johnpolakow/PI_Blackbox/Docs/Diagrams/Single_Pi.pdf

## Single Raspberry Pi

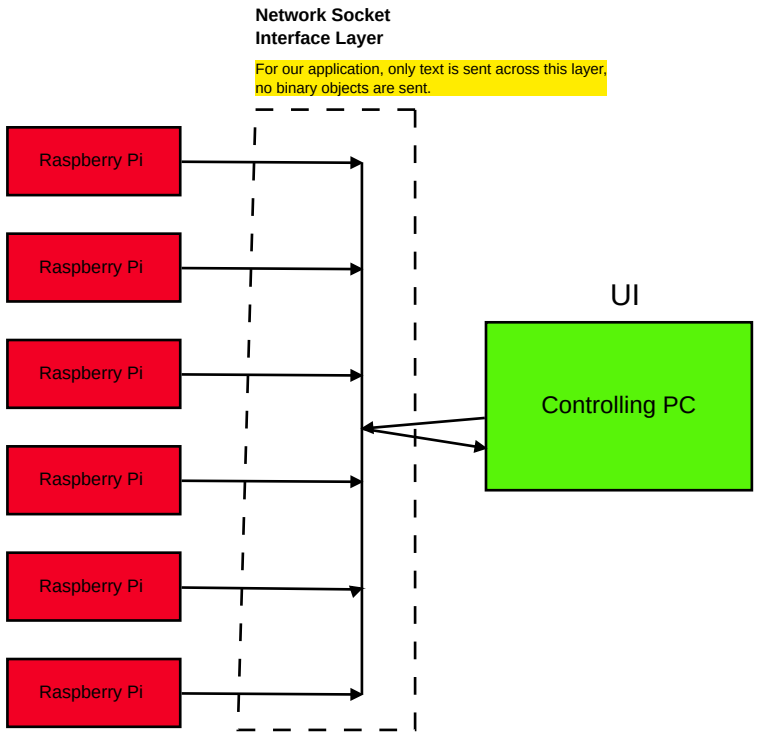
[picture p5: figure]
Raspberry Pi; Controlling PC; Network Socket Interface Layer; no binary objects are sent.

## Controlling PC

## Pis networked together via Ethernet or Wifi

For our application, only text is sent across this layer,

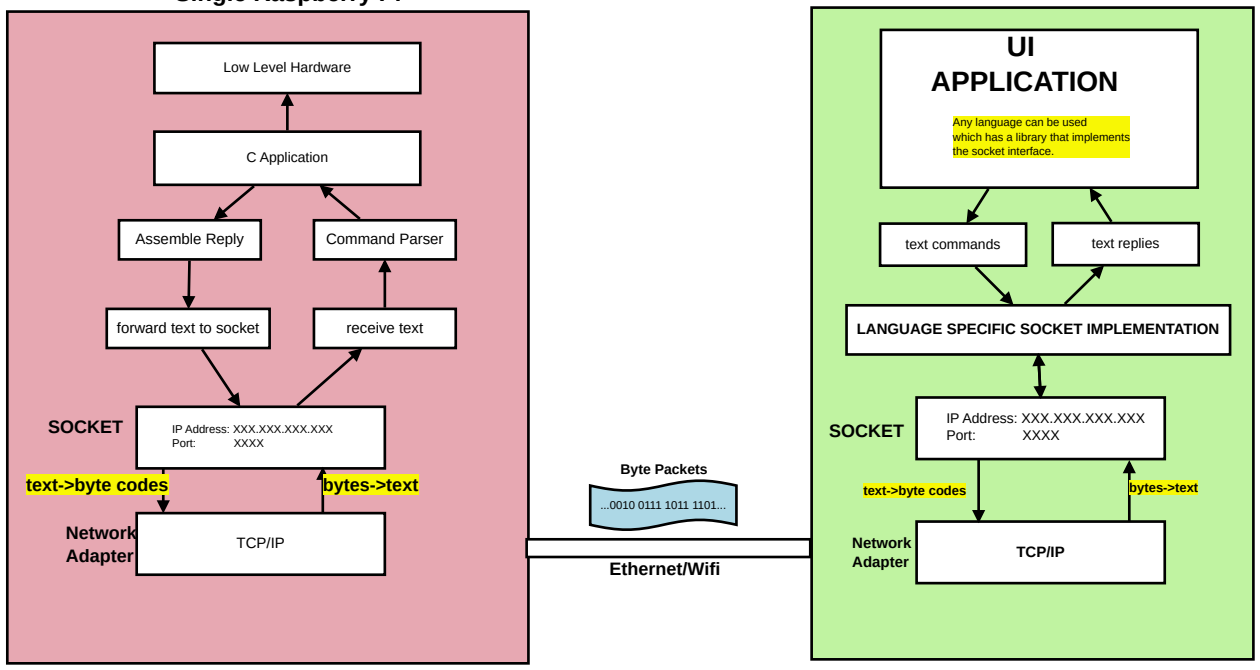
[picture p6: figure]
Low Level Hardware; C Application; Command Parser; receive text; Assemble Reply; forward text to socket; SOCKET; IP Address: XXX.XXX.XXX.XXX; Port:; XXXX; TCP/IP Network Adapter; text->byte codes; TCP/IP; bytes->text; Network Adapter; Byte Packets; Ethernet/Wifi; UI APPLICATION; text commands; text replies; LANGUAGE SPECIFIC SOCKET IMPLEMENTATION; Any language can be used which has a library that implements the socket interface.
