johnpolakow/PI_Blackbox/md/netstat_l_46.png

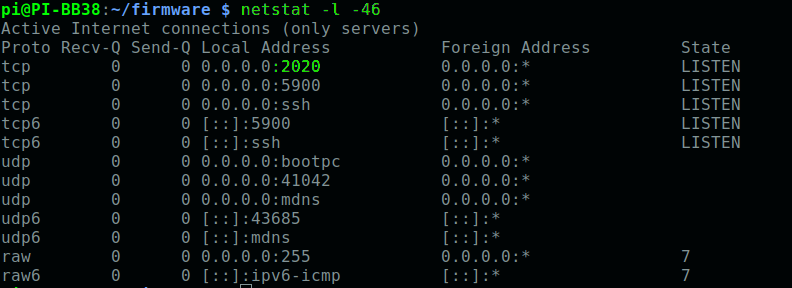
md/netstat_l_46.png
