johnpolakow/PI_Blackbox/PI_Firmware/Configuration/conf_files/images/72.jpeg

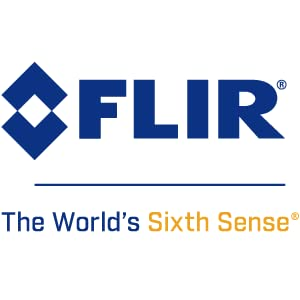
PI_Firmware/Configuration/conf_files/images/72.jpeg
