johnpolakow/PI_Blackbox/PI_Firmware/Configuration/conf_files/images/BlackPi.jpg

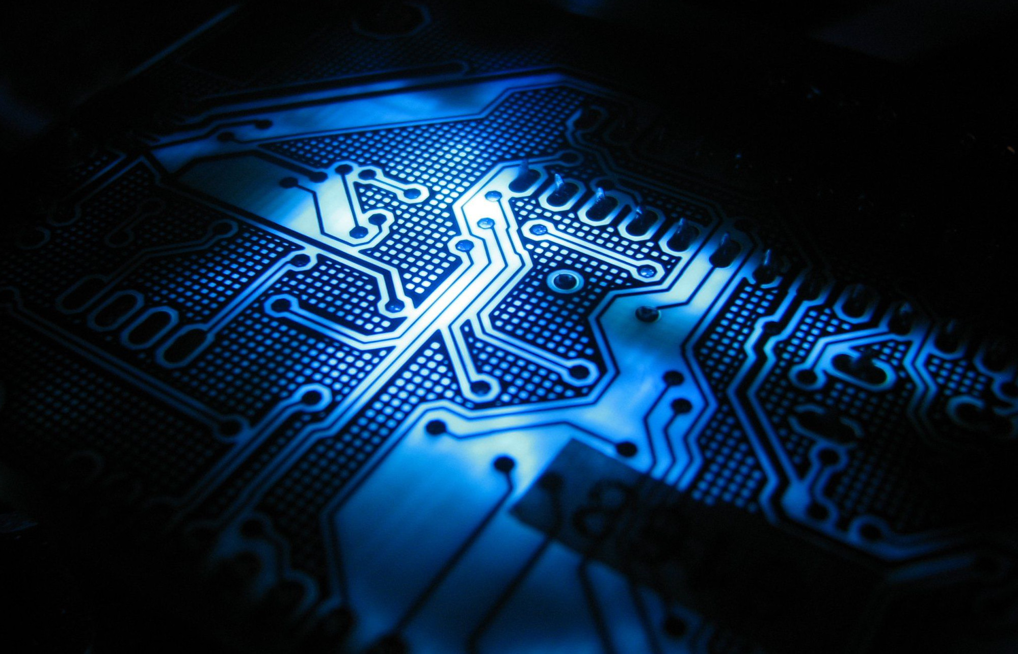
PI_Firmware/Configuration/conf_files/images/BlackPi.jpg
