johnpolakow/PI_Blackbox/PI_Firmware/Configuration/conf_files/images/geometry.jpg

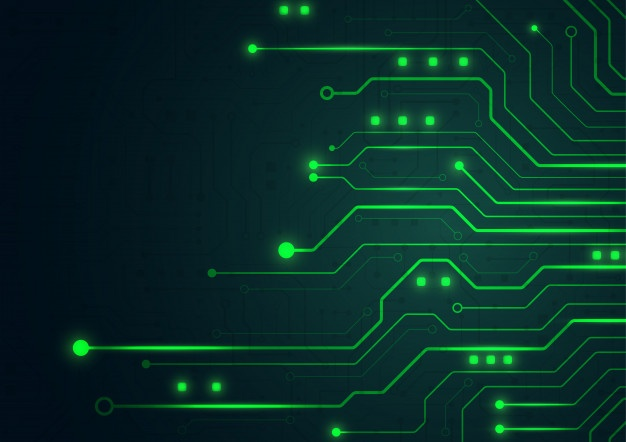
PI_Firmware/Configuration/conf_files/images/geometry.jpg
