johnpolakow/PI_Blackbox/PI_Firmware/Configuration/conf_files/images/glow2pi.jpg

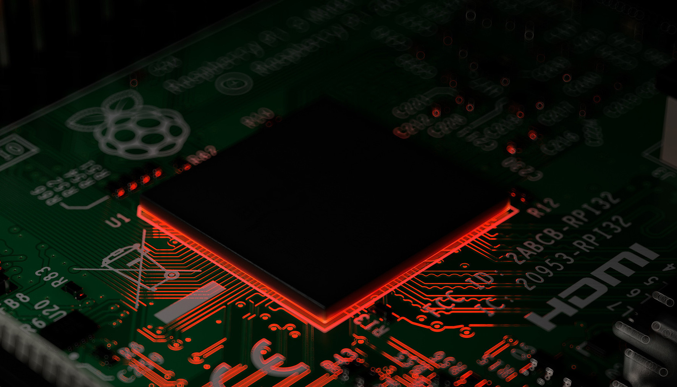
PI_Firmware/Configuration/conf_files/images/glow2pi.jpg
