johnpolakow/PI_Blackbox/PI_Firmware/Configuration/conf_files/images/landscape.png

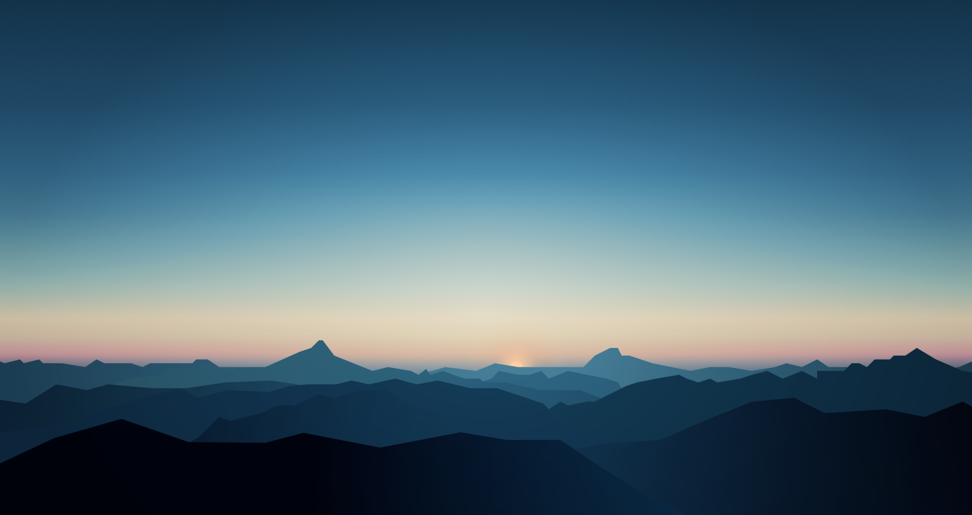
PI_Firmware/Configuration/conf_files/images/landscape.png
