johnpolakow/PI_Blackbox/PI_Firmware/Configuration/conf_files/images/unnamed1.jpg

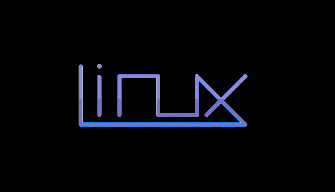
PI_Firmware/Configuration/conf_files/images/unnamed1.jpg
