johnpolakow/PI_Blackbox/PCB/Cal_Station/Cal_Station.pdf

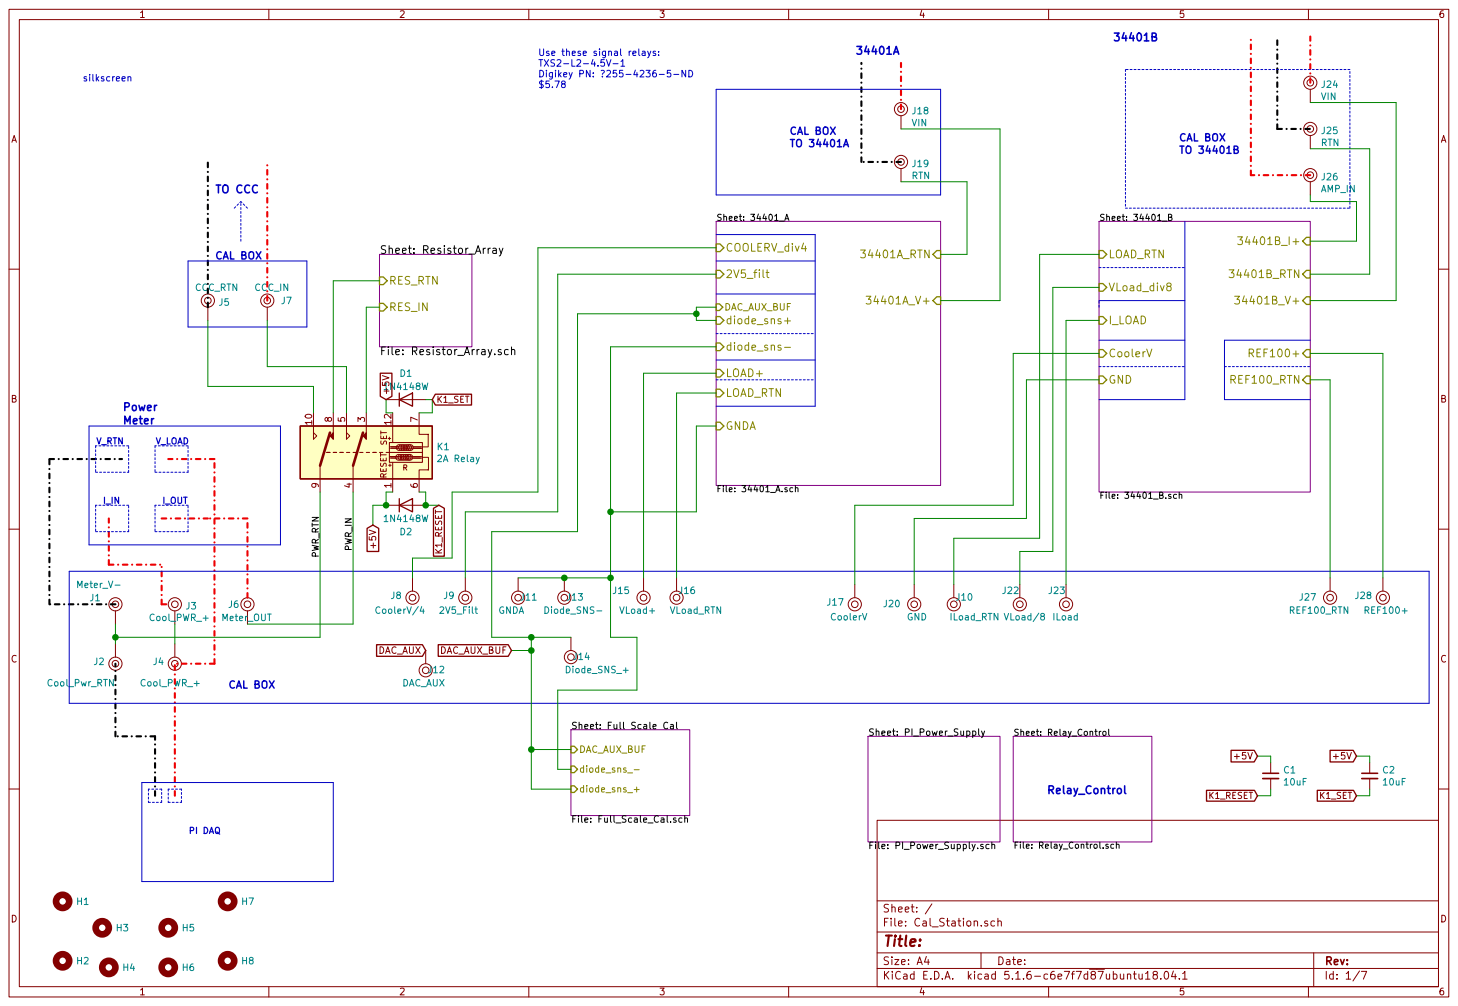
[picture p33: page 1]

CAL BOX

34401A_V+ DAC_AUX_BUF Sheet: Full Scale Cal File: Full_Scale_Cal.sch

File: Cal_Station.sch Sheet: / Sheet: PI_Power_Supply

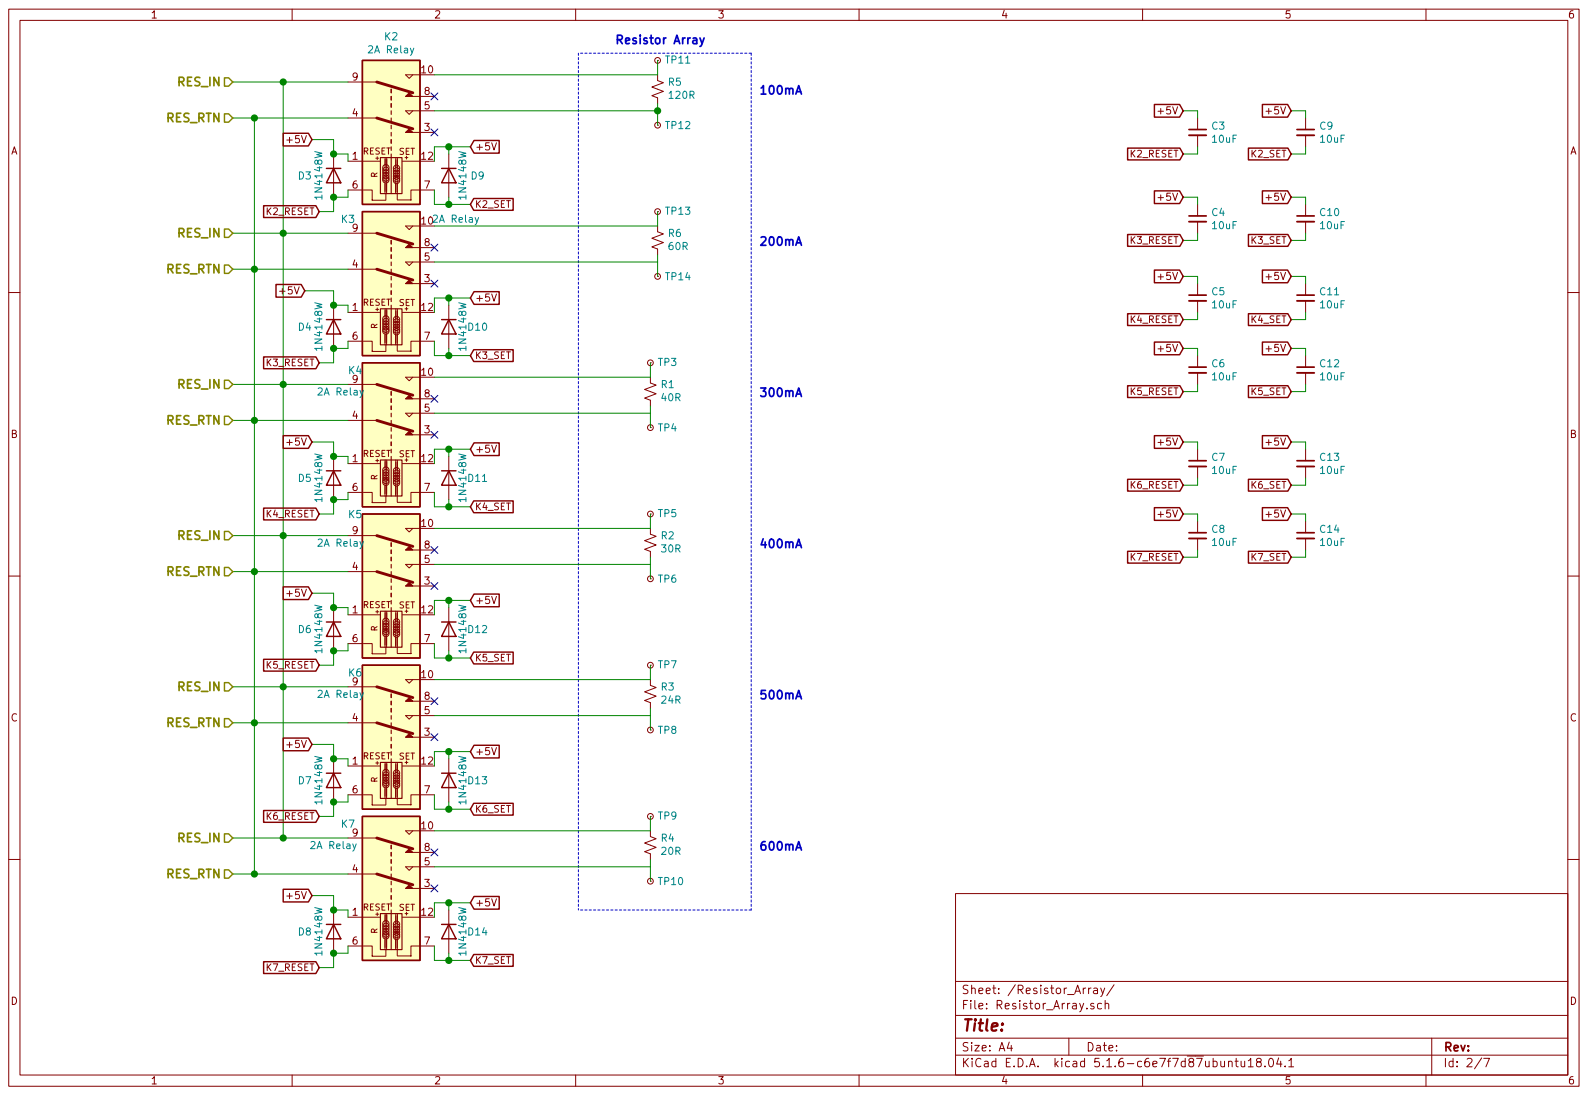
[picture p34: page 2]

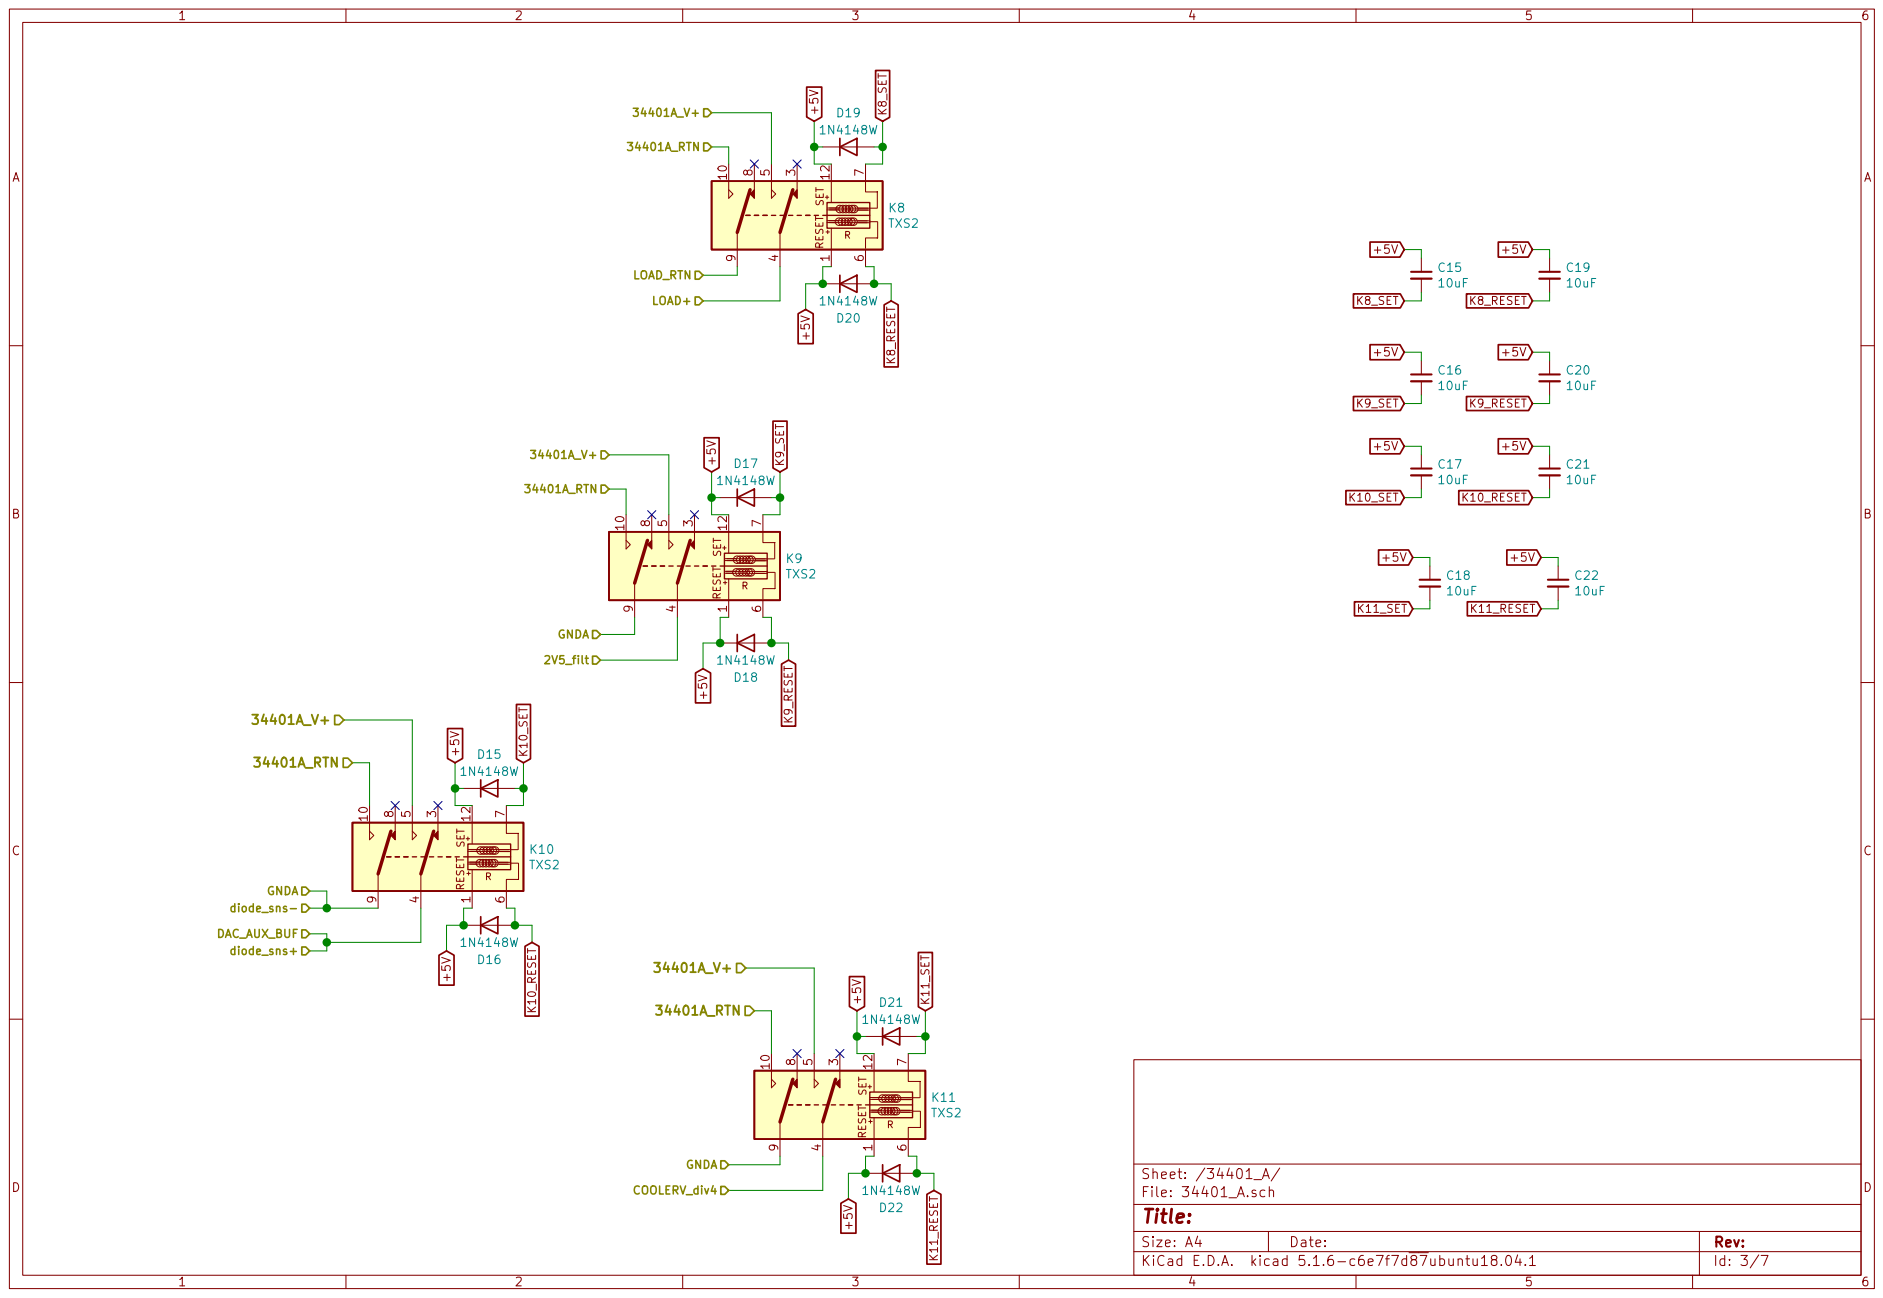
[picture p35: page 3]

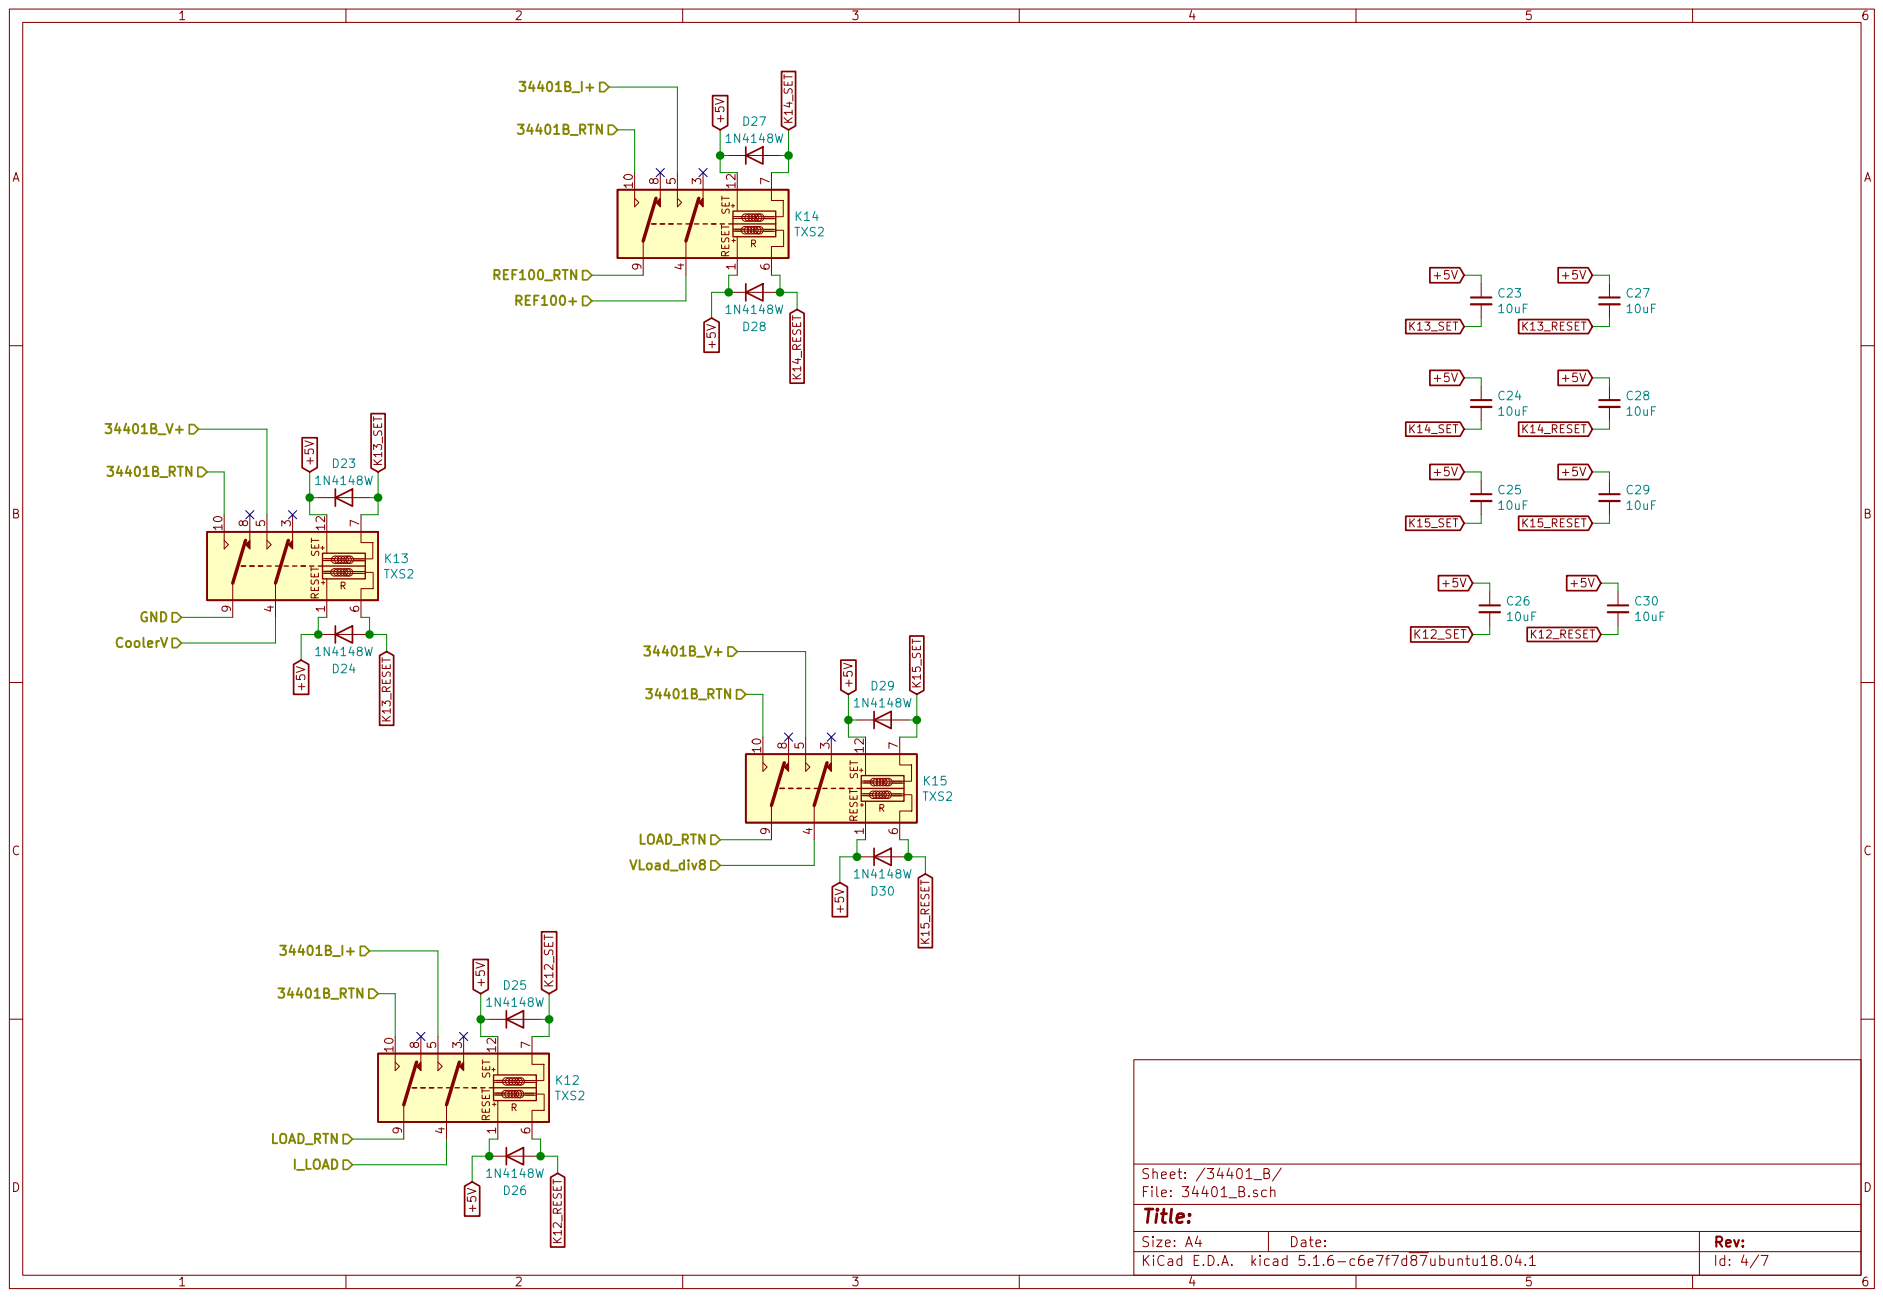
[picture p36: page 4]

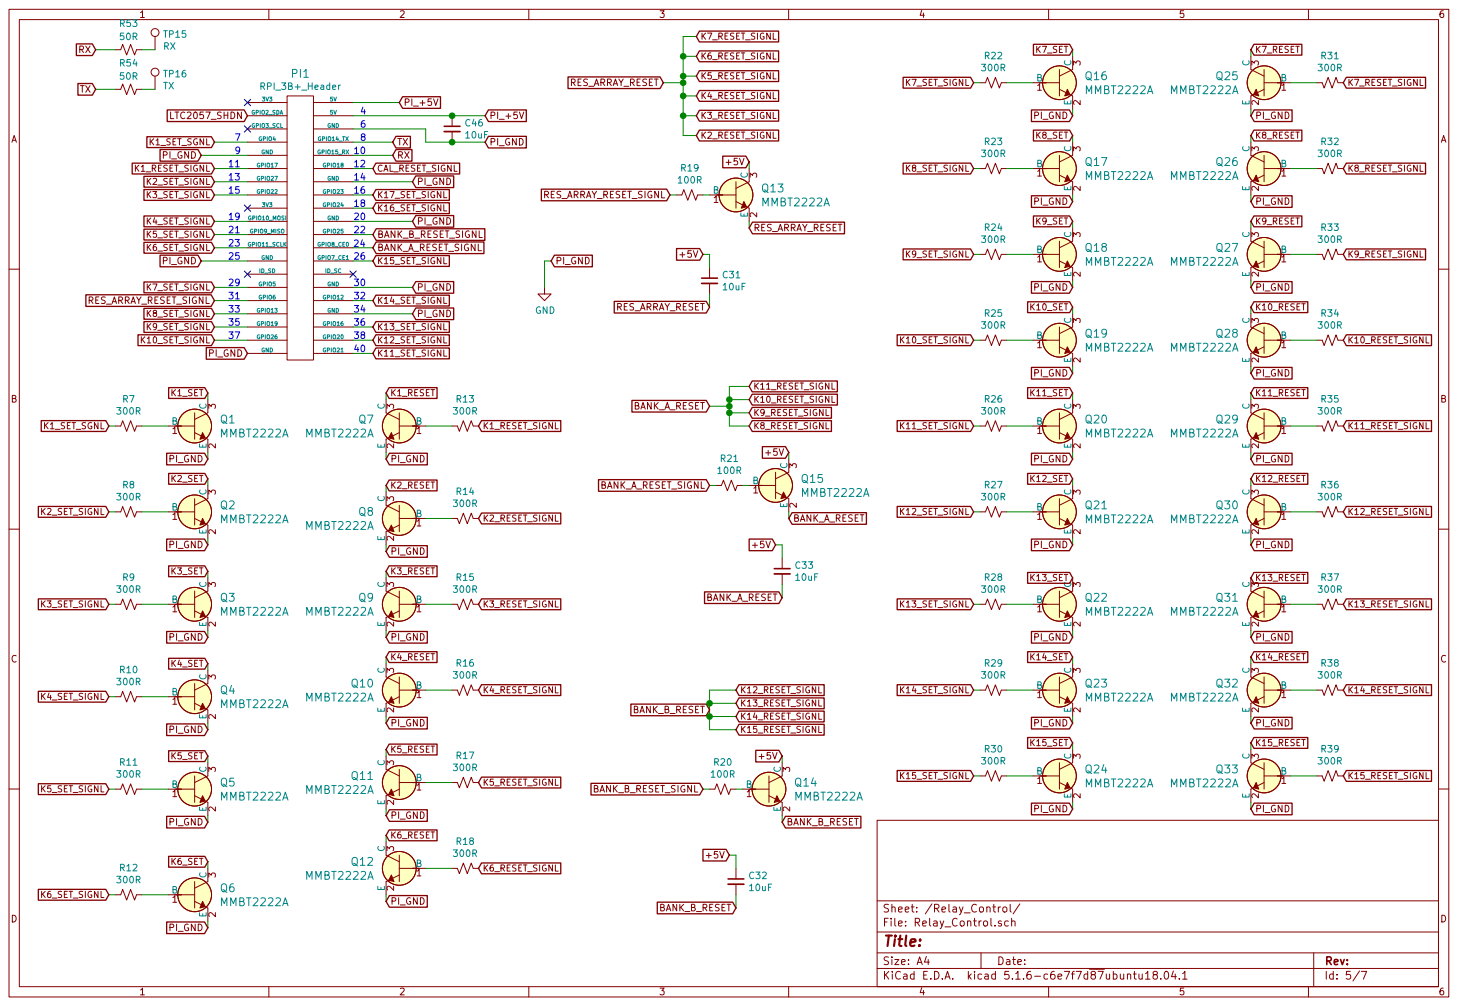
[picture p37: page 5]

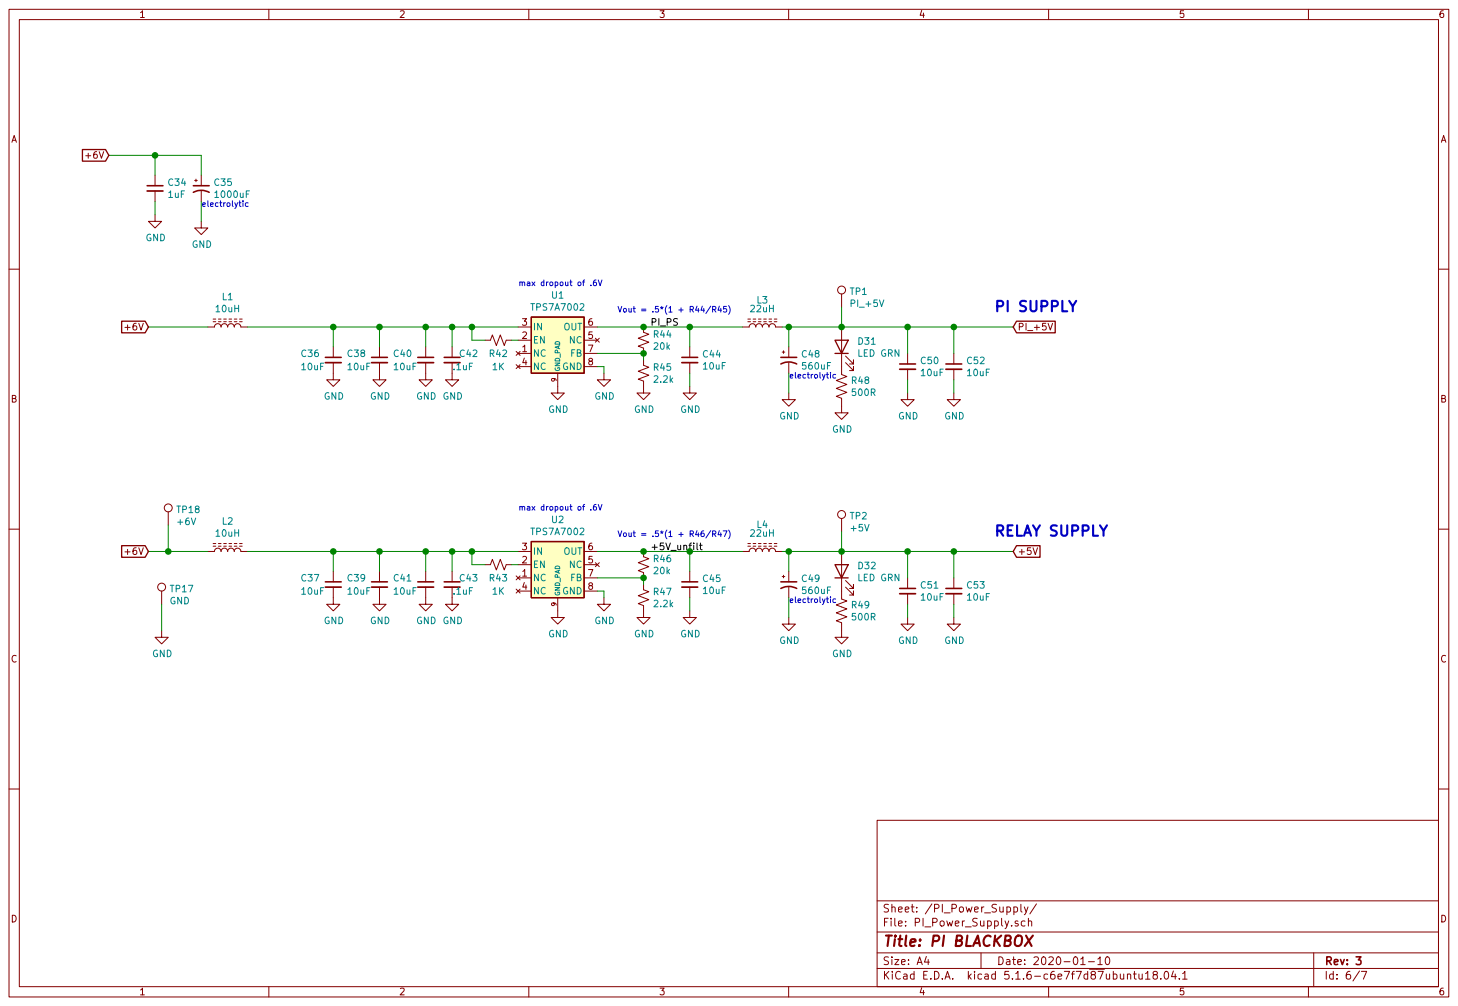
[picture p38: page 6]

max dropout of .6V

File: PI_Power_Supply.sch
Id: 6/7 Title: PI BLACKBOX

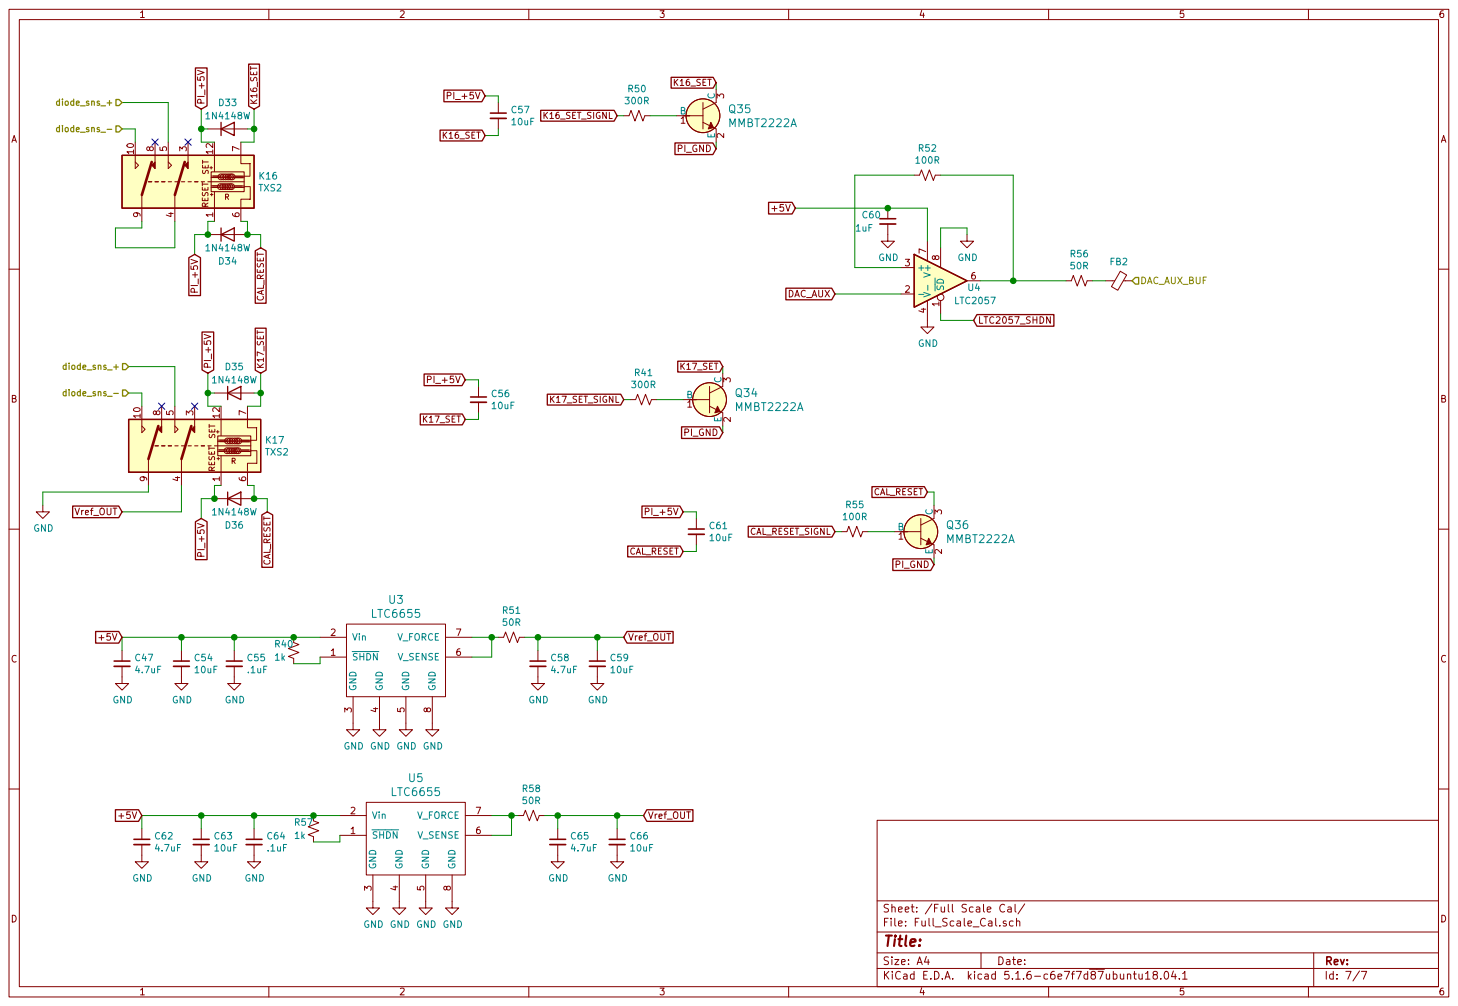
[picture p39: page 7]

100R GND GND GND GND
