johnpolakow/PI_Blackbox/PCB/Cal_Station/FAB/Board_Outline.pdf

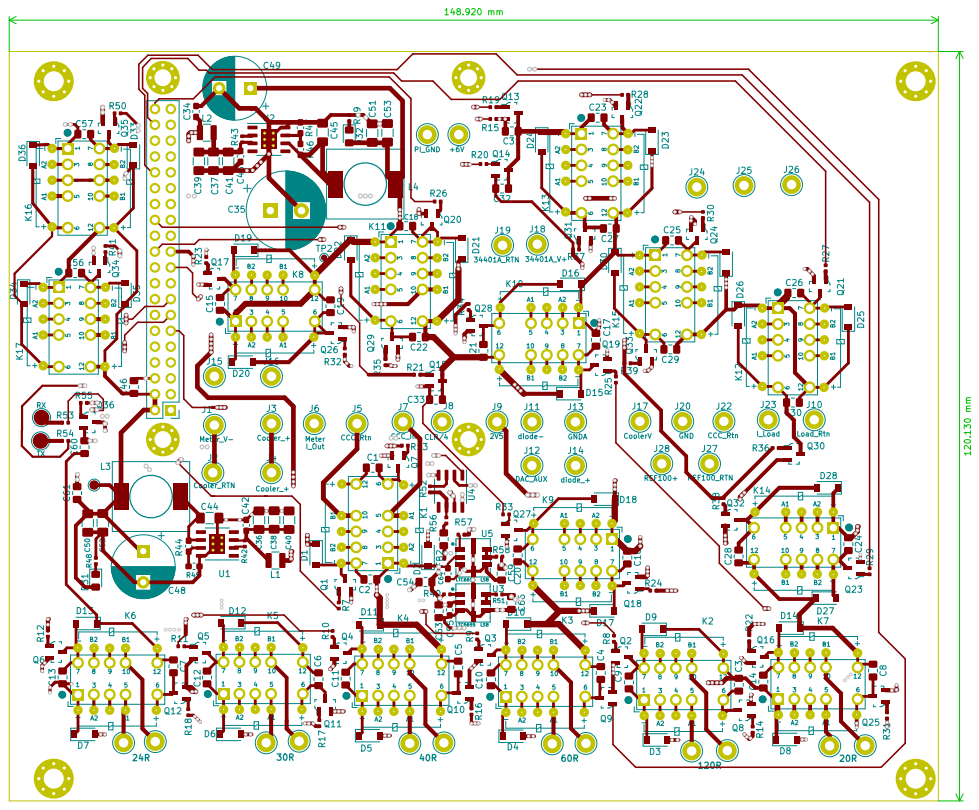
[picture p42: page 1]
