johnpolakow/PI_Blackbox/PI_Firmware/Release0/clientserver.h

#ifndef __CLIENTSERVER_H
#define __CLIENTSERVER_H

#include <stdio.h>
#include <stdlib.h>
#include <unistd.h>
#include <errno.h>
#include <string.h>
#include <sys/types.h>
#include <sys/socket.h>
#include <netinet/in.h>
#include <netdb.h>
#include <arpa/inet.h>
#include <sys/wait.h>
#include <signal.h>
#include <assert.h>
#include <sys/time.h>
#include "colors.h"


// a convenience struct that contains the socket and remote address for a connection
typedef struct {
	int sockfd;
	struct sockaddr_in theiraddr;
} conn_t;


conn_t* connect_tcp(const char* serverIP, const char* serverPort);
void disconnect_tcp(conn_t* connxn);
conn_t* listen_tcp(const char* listenPort);
conn_t* accept_tcp(conn_t* listenconn);
int recv_tcp(conn_t* connxn, char* buffer, unsigned int bufSize);
int send_tcp(conn_t* connxn, char* buffer, unsigned int bytesToSend);
int recvData(conn_t* connxn, char* buffer, unsigned int bufSize);
int sendData(conn_t* connxn, char* buffer, unsigned int bytesToSend);





#define BACKLOG	5


// Connect to IP:port, allocate any necessary resources
conn_t* connect_tcp(const char* server_IP, const char* server_Port) {
	struct addrinfo hints;
	struct addrinfo *result = NULL;
	memset(&hints, 0, sizeof(hints));
	hints.ai_family = AF_INET;
	hints.ai_socktype = SOCK_STREAM;
	hints.ai_flags = AI_PASSIVE;

	conn_t* server_conn = (conn_t*)malloc(sizeof(conn_t));

	int status = getaddrinfo(server_IP, server_Port, &hints, &result);
	if (status != 0)
	{
		fprintf(stderr, "getaddrinfo error: %s\n", gai_strerror(status));
		return NULL;
	}

	server_conn->sockfd = socket(result->ai_family, result->ai_socktype, result->ai_protocol);

	status = connect(server_conn->sockfd, result->ai_addr, result->ai_addrlen);

	return server_conn;
}

// Disconnect socket, free any allocated resources
void disconnect_tcp(conn_t* connxn)
{
	close(connxn->sockfd);
	free(connxn);
}

// Listen on given port
conn_t* listen_tcp(const char* listenPort) {
	int yes=1;
	struct addrinfo hints;
	struct addrinfo *result = NULL, *p;
	conn_t* listenconn = (conn_t*)malloc(sizeof(conn_t));  // listen on sock_fd, new connection on new_fd

	memset(&hints, 0, sizeof(hints));
	hints.ai_family = AF_INET;
	hints.ai_socktype = SOCK_STREAM;
	hints.ai_flags = AI_PASSIVE;

	int status = getaddrinfo(NULL, listenPort, &hints, &result);
	if (status != 0) {
		fprintf(stderr, "getaddrinfo error: %s\n", gai_strerror(status));
		return NULL;
	}

	// loop through all the results and bind to the first we can
	for(p = result; p != NULL; p = p->ai_next) {
		if ((listenconn->sockfd = socket(p->ai_family, p->ai_socktype,
							 p->ai_protocol)) == -1) {
			perror("could not create socket with this address, retrying...\n");
			continue;
		}

		if (setsockopt(listenconn->sockfd, SOL_SOCKET, SO_REUSEADDR, &yes,
						sizeof(int)) == -1) {
			perror("setsockopt on this socket failed, retrying...\n");
			continue;//return -1;
		}

		if (bind(listenconn->sockfd, p->ai_addr, p->ai_addrlen) == -1) {
			close(listenconn->sockfd);
			perror("bind on this address failed, retrying...\n");
			continue;
		}

		break;
	}

	if (p == NULL) {
		fprintf(stderr, "failed to bind\n");
		return NULL;
	}

	freeaddrinfo(result); // all done with this structure

	if (listen(listenconn->sockfd, BACKLOG) == -1) {
		perror("could not listen\n");
		return NULL;
	}

	return listenconn;
}

// wait for (blocking) and accept any incoming connections on the listening socket
conn_t* accept_tcp(conn_t* listenconn) {
	char s[INET6_ADDRSTRLEN];
	socklen_t sin_size;
	struct sockaddr_in their_addr;
	sin_size = sizeof(their_addr);

	conn_t* clientconn = (conn_t*)malloc(sizeof(conn_t));

	clientconn->sockfd = accept(listenconn->sockfd, (struct sockaddr*)&their_addr, &sin_size);
	if (clientconn->sockfd == -1) {
		perror("accept failed\n");
		return NULL;
	}
	clientconn->theiraddr = their_addr;

	inet_ntop(AF_INET, &(their_addr.sin_addr), s, sizeof(s));

	printf("Accepted connection from:  " COLOR_BOLD_GREEN "%s\n\n" COLOR_RESET, s);
	return clientconn;
}

// receive data on the socket
int recv_tcp(conn_t* connxn, char* buffer, unsigned int bufSize) {
	int retVal = recv(connxn->sockfd, buffer, bufSize, 0);
	if(retVal <= 0) {
		if(retVal == 0)
			printf("other party disconnected\n");
		else
			printf("Error in socket recv %s\n",gai_strerror(retVal));
	}

	return retVal;
}

// send data on the socket
int send_tcp(conn_t* connxn, char* buffer, unsigned int bytesToSend) {
	int ret;
	int retVal = 0;

	if( bytesToSend == 0 )
			return 0;
	// all data in the buffer may not be sent on a single call to send(),
	// so loop until all data is sent
	while (retVal < (int)bytesToSend) {
		ret = send(connxn->sockfd, (char*)(buffer+retVal), bytesToSend-retVal, 0);
		if( ret <= 0 ) {
			printf("error in send\n");
			retVal = ret;
			break;
		}
		retVal += ret;
	}

	return retVal;
}

// Convenience function: Receive data into a provided buffer on the given connection
int recvData(conn_t* connxn, char* buffer, unsigned int bufSize) {
	int retVal = recv_tcp(connxn, (char*)buffer, bufSize);
	if (retVal <= 0) {
		disconnect_tcp(connxn);
	}
	return retVal;
}

// Convenience function: Send data in a provided buffer on the given connection
int sendData(conn_t* connxn, char* buffer, unsigned int bytesToSend) {
	int retVal = send_tcp(connxn, (char*)buffer, bytesToSend);
	if (retVal <= 0) {
		disconnect_tcp(connxn);
	}
	return retVal;
}










#endif
