johnpolakow/PI_Blackbox/PI_Firmware/Configuration/src/colors.h

#define COLOR_RED "\x1b[31m"
#define COLOR_GREEN "\x1b[32m"
#define COLOR_YELLOW "\x1b[33m"
#define COLOR_BLUE "\x1b[34m"
#define COLOR_MAGENTA "\x1b[35m"
#define COLOR_CYAN "\x1b[36m"
#define COLOR_BROWN "\033[22;33m"
#define COLOR_GRAY "\033[22;37m"
#define COLOR_LIGHT_RED "\033[01;31m"
#define COLOR_LIGHT_GREEN "\033[01;32m"
#define COLOR_LIGHT_CYAN "\033[01;36m"
#define COLOR_LIGHT_MAGENTA "\033[01;35m"
#define COLOR_LIGHT_BLUE "\033[01;34m"
#define COLOR_RESET "\x1b[0m"

#define LINE_SEPARATOR  "------------------------------------------------------------------------------\n"




//  High Intensity
#define COLOR_BRIGHT_GREEN  "\033[0;92m"
#define COLOR_BRIGHT_YELLOW "\033[0;93m"
#define COLOR_BRIGHT_BLUE   "\033[0;94m"
#define COLOR_BRIGHT_MAGENTA "\033[0;95m"
#define COLOR_BRIGHT_CYAN   "\033[0;96m"
#define COLOR_BRIGHT_WHITE  "\033[0;97m"



#define COLOR_BOLD_RED      "\033[1;91m"
#define COLOR_BOLD_GREEN    "\033[1;92m"
#define COLOR_BOLD_YELLOW   "\033[1;93m"
#define COLOR_BOLD_BLUE   "\033[1;94m"
#define COLOR_BOLD_MAGENTA  "\033[1;95m"
#define COLOR_BOLD_CYAN     "\033[1;96m"
#define COLOR_BOLD_WHITE    "\033[1;97m"


/*
# Underline
UBlack='\033[4;30m'       # Black
URed='\033[4;31m'         # Red
UGreen='\033[4;32m'       # Green
UYellow='\033[4;33m'      # Yellow
UBlue='\033[4;34m'        # Blue
UPurple='\033[4;35m'      # Purple
UCyan='\033[4;36m'        # Cyan
UWhite='\033[4;37m'       # White

# Background
On_Black='\033[40m'       # Black
On_Red='\033[41m'         # Red
On_Green='\033[42m'       # Green
On_Yellow='\033[43m'      # Yellow
On_Blue='\033[44m'        # Blue
On_Purple='\033[45m'      # Purple
On_Cyan='\033[46m'        # Cyan
On_White='\033[47m'       # White




*/
