johnpolakow/PI_Blackbox/PI_Firmware/Release0/TODO.h

//
///
/*



Toggle Current Source


write commands to log file


status command- if test is running, it reports relay state and load set value & test running time
stop test - return log file name
send log integration
read & set DS3231

mutexes on MAX31856

    // for all tests but lifetime & custom, verify there is a stop test time
    // verify all profile times are successive

Verify_DUT_IDs_Set
GUI integration
record commands to log file after executing in socket receive
DS3231 time


ASCII code 248 = ° ( Degree symbol )
ASCII code 179 = │ ( Box drawing character single vertical line )
ASCII code 192 = └ ( Box drawing character single line lower left corner )
ASCII code 195 = ├ ( Box drawing character single line vertical and right )
ASCII code 196 = ─ ( Box drawing character single horizontal line )
SCII code 174 = « ( Angle quotes, guillemets, right-pointing quotation mark )
ASCII code 175 = » ( Guillemets, angle quotes, left-pointing quotation marks )
ASCII code 254 = ■ ( black square )
ASCII code 186 = ║ ( Box drawing character double vertical line )
ASCII code 187 = ╗ ( Box drawing character double line upper right corner )
ASCII code 188 = ╝ ( Box drawing character double line lower right corner )
Ohms 234
micro 230
square root 251
+- 241
~ 247
thick corners: 220-224

˥˦˧˨˩˪˫

°±²³µ¼½¾ ÷øɸ

U+00B5	µ	0181	&micro;	Micro sign
U+00B0	°	0176	&deg;	Degree symbol
	U+00D7	×	0215	&times;	Multiplication sign
  U+00F7	÷	0247	&divide;	Division sign
  U+00F8	ø	0248	&oslash;	Latin Small Letter O with stroke
  U+03A6	Φ	934	Greek Capital Letter Phi
  U+0398	Θ	920	Greek Capital Letter Theta
  U+03A3	Σ	931	Greek Capital Letter Sigma
  U+03A6	Φ	934	Greek Capital Letter Phi
  U+03A8	Ψ	936	Greek Capital Letter Psi
  U+03A9	Ω	937	Greek Capital Letter Omega
  U+03BC	μ	956	Greek Small Letter Mu
  U+03C0	π	960	Greek Small Letter Pi
  U+03C4	τ	964	Greek Small Letter Tau
  ? with box around it 2370
  X rectangle in a box 2327
  curved corners  256D, 256E, 256F, 2570, 2577, 2575, 258E,
  2386 enter symbol
  attention triangle 25B2
  warning sign 26A0
  X mark 274C
  Heavy ! 2757
  data connected 2B80
  mA 3383
  Hz 3390
  mV 33B7
  mW 33BD
  ms 33B3
  DC 2393

  degC = 2103



*/
